DreaM117er/Explorer-Keyboard-RxCT/files/mcu/left-mcu base.stl

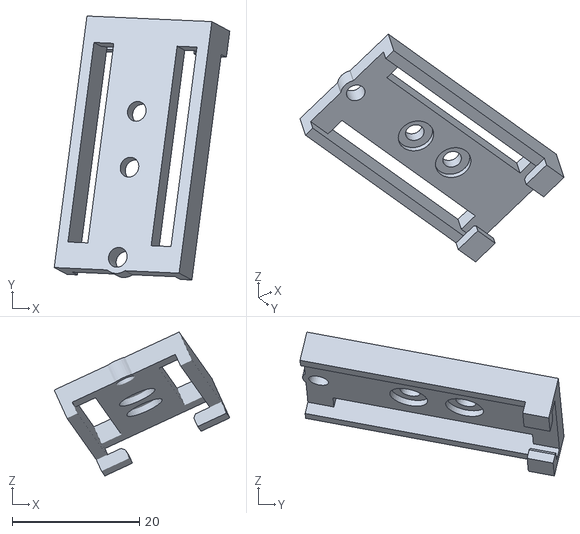
[picture p52: CAD file, 2023-04-23]
files/mcu/left-mcu base.stl
27.6 x 41.6 x 22.7
