DreaM117er/Explorer-Keyboard-RxCT/files/battery/left-box 602050.stl

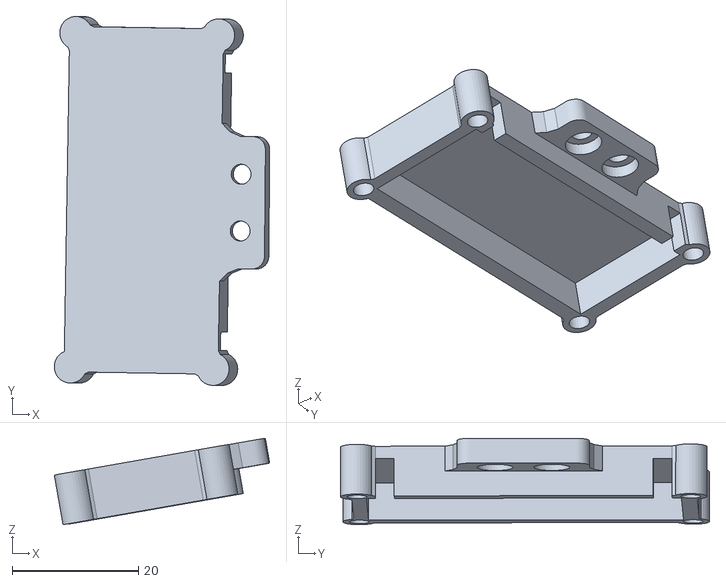
[picture p53: CAD file, 2023-04-23]
files/battery/left-box 602050.stl
34.2 x 58.6 x 13.7
