DreaM117er/Explorer-Keyboard-RxCT/files/mcu/right-trrs stuck.stl

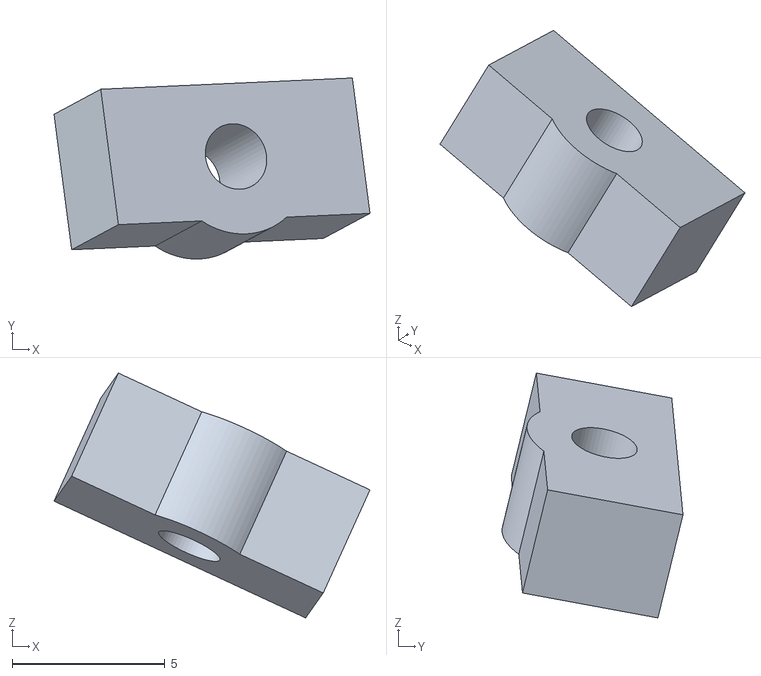
[picture p54: CAD file, 2023-04-23]
files/mcu/right-trrs stuck.stl
10.4 x 5.93 x 8.03
