DreaM117er/Explorer-Keyboard-RxCT/files/thumb/left-thumb area basepart.stl

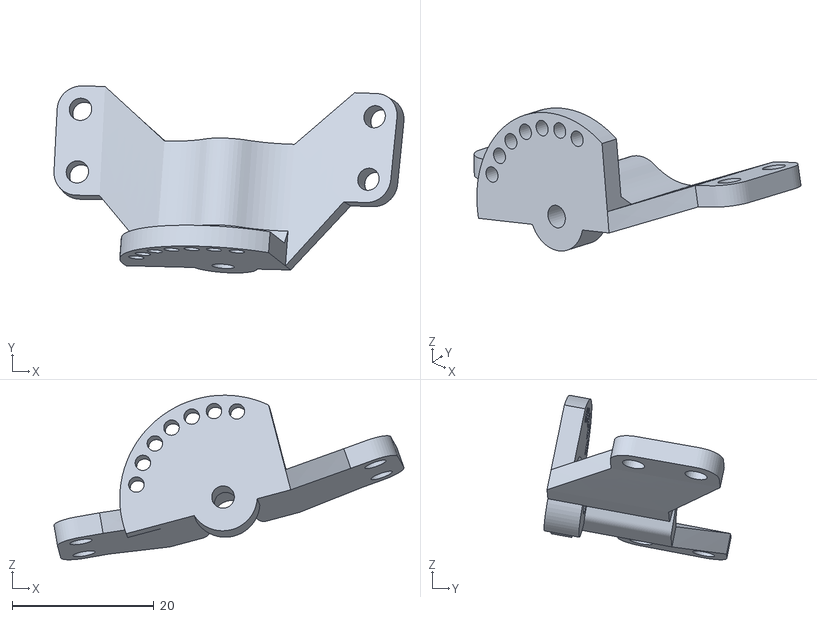
[picture p55: CAD file, 2023-04-23]
files/thumb/left-thumb area basepart.stl
49.4 x 26.4 x 23.2
