DreaM117er/Explorer-Keyboard-RxCT/files/battery/left-box 802050.stl

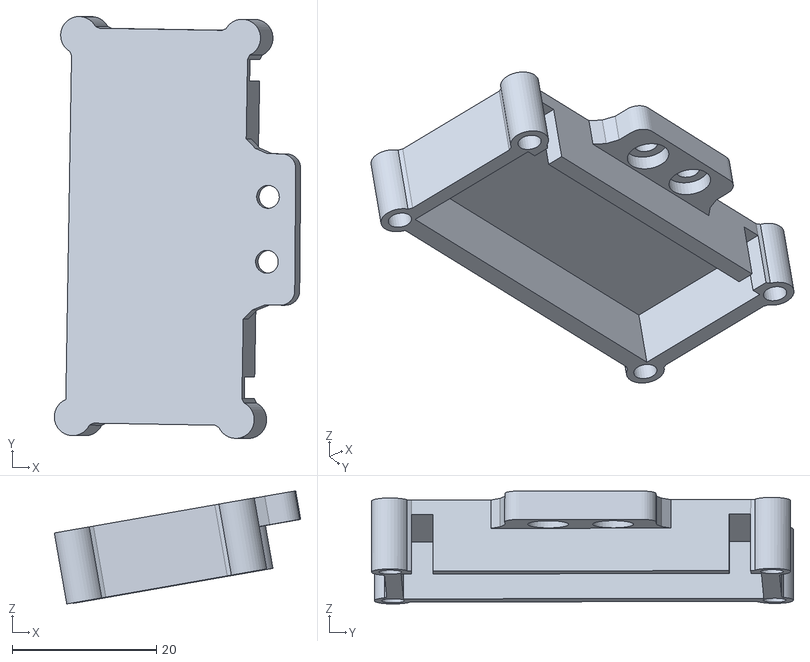
[picture p56: CAD file, 2023-04-23]
files/battery/left-box 802050.stl
34.2 x 58.6 x 15.7
