DreaM117er/Explorer-Keyboard-RxCT/files/thumb/linker.stl

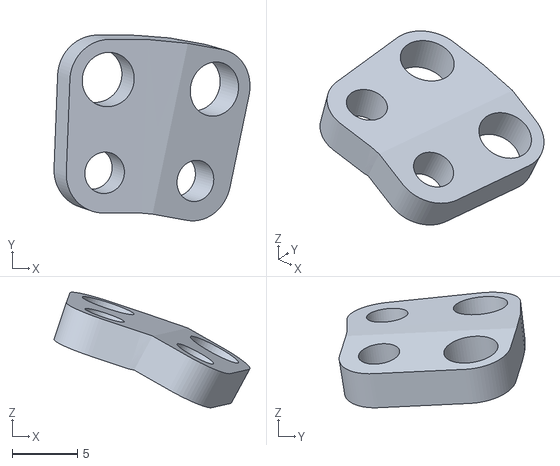
[picture p57: CAD file, 2023-04-23]
files/thumb/linker.stl
15.0 x 14.3 x 8.87
