DreaM117er/Explorer-Keyboard-RxCT/files/right-3x5 bottom case.stl

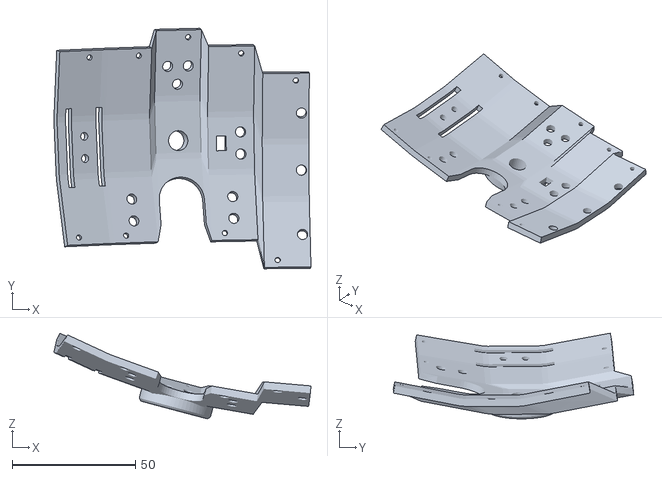
[picture p58: CAD file, 2023-04-23]
files/right-3x5 bottom case.stl
104.4 x 97.8 x 34.8
