DreaM117er/Explorer-Keyboard-RxCT/files/thumb/left-thumb AA plate.stl

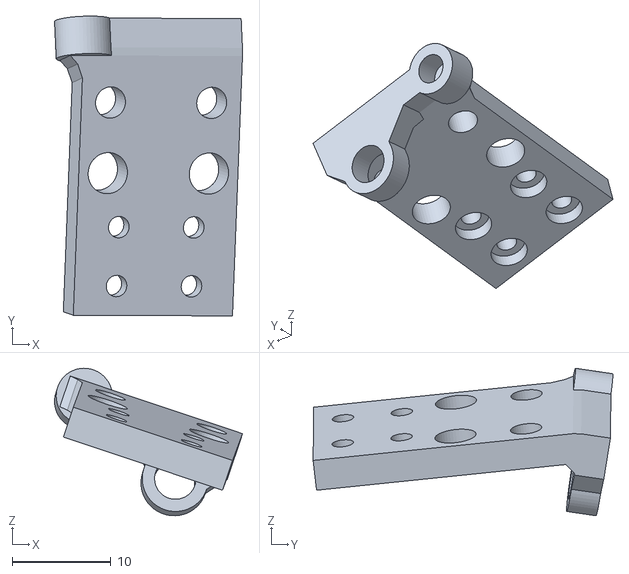
[picture p59: CAD file, 2023-04-23]
files/thumb/left-thumb AA plate.stl
19.0 x 30.4 x 14.9
