DreaM117er/Explorer-Keyboard-RxCT/files/3x1-column.stl

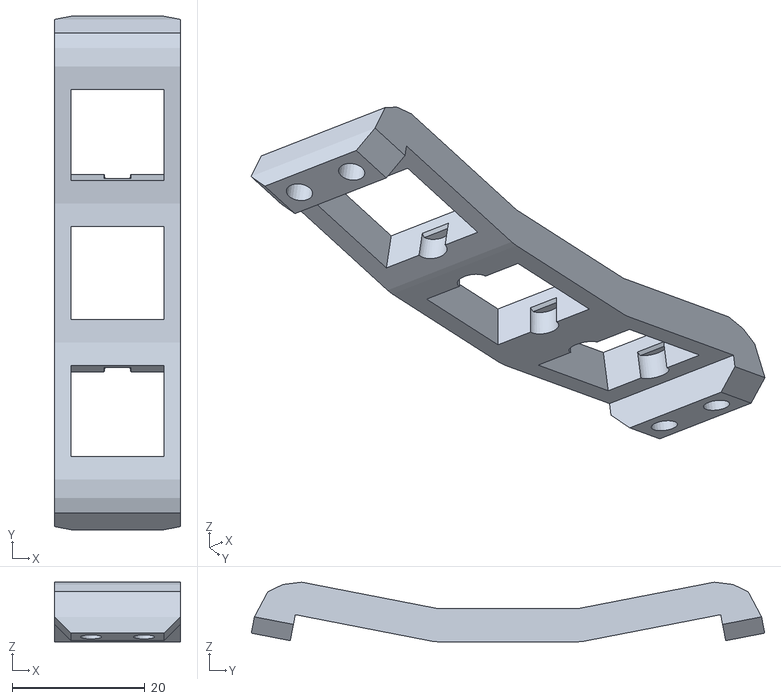
[picture p60: CAD file, 2023-04-23]
files/3x1-column.stl
19.0 x 77.5 x 9.01
