DreaM117er/Explorer-Keyboard-RxCT/files/right-3x1 bottom expand case.stl

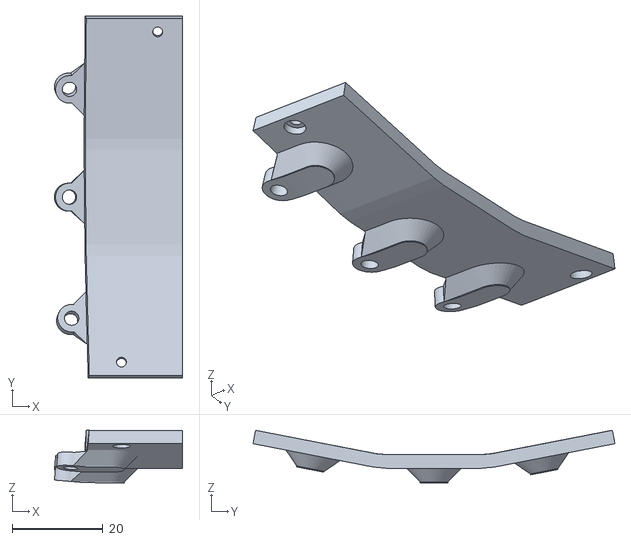
[picture p61: CAD file, 2023-04-23]
files/right-3x1 bottom expand case.stl
28.3 x 79.9 x 11.6
