DreaM117er/Explorer-Keyboard-RxCT/files/thumb/x1-thumb plate.stl

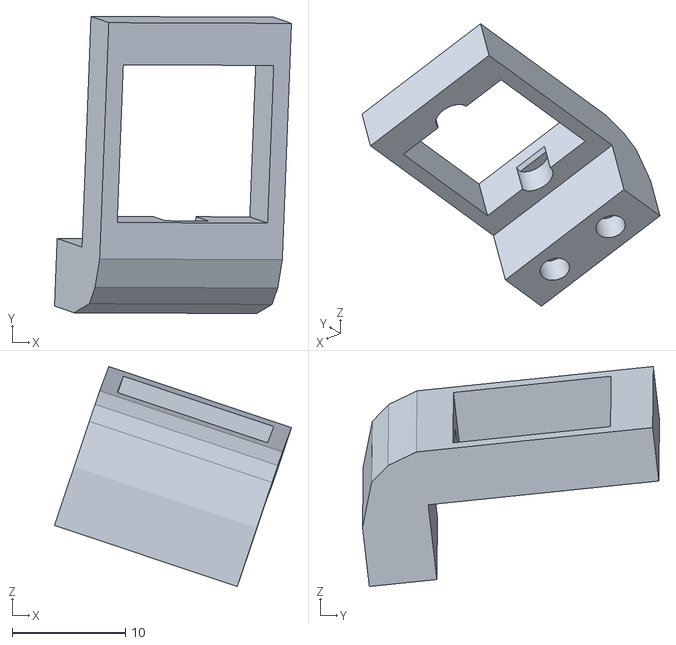
[picture p62: CAD file, 2023-04-23]
files/thumb/x1-thumb plate.stl
20.9 x 26.2 x 19.4
