DreaM117er/Explorer-Keyboard-RxCT/files/right-front basepart.stl

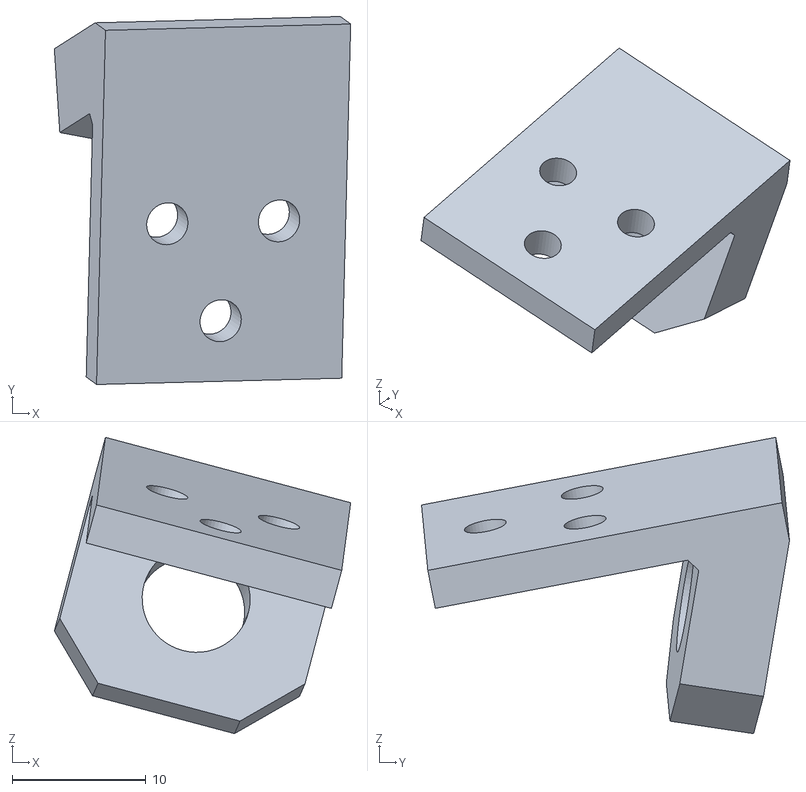
[picture p63: CAD file, 2023-04-23]
files/right-front basepart.stl
22.2 x 27.6 x 22.2
