DreaM117er/Explorer-Keyboard-RxCT/files/4x1-column.stl

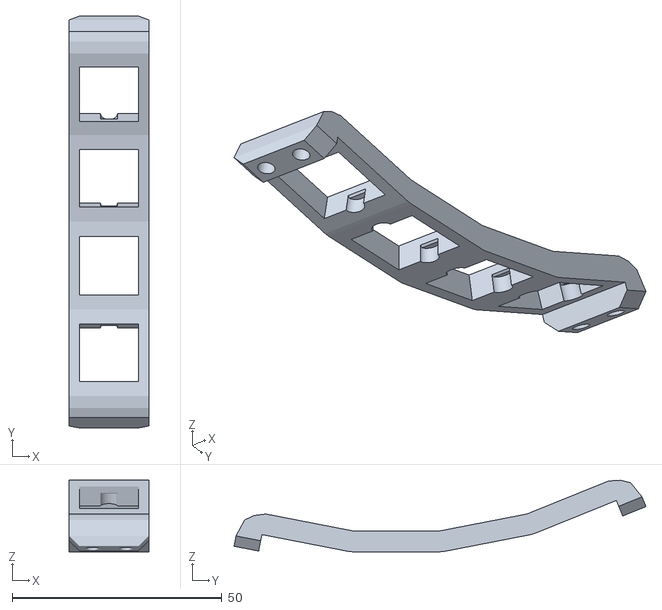
[picture p64: CAD file, 2023-04-23]
files/4x1-column.stl
19.0 x 98.3 x 17.1
