DreaM117er/Explorer-Keyboard-RxCT/image/guide/6-46.jpg

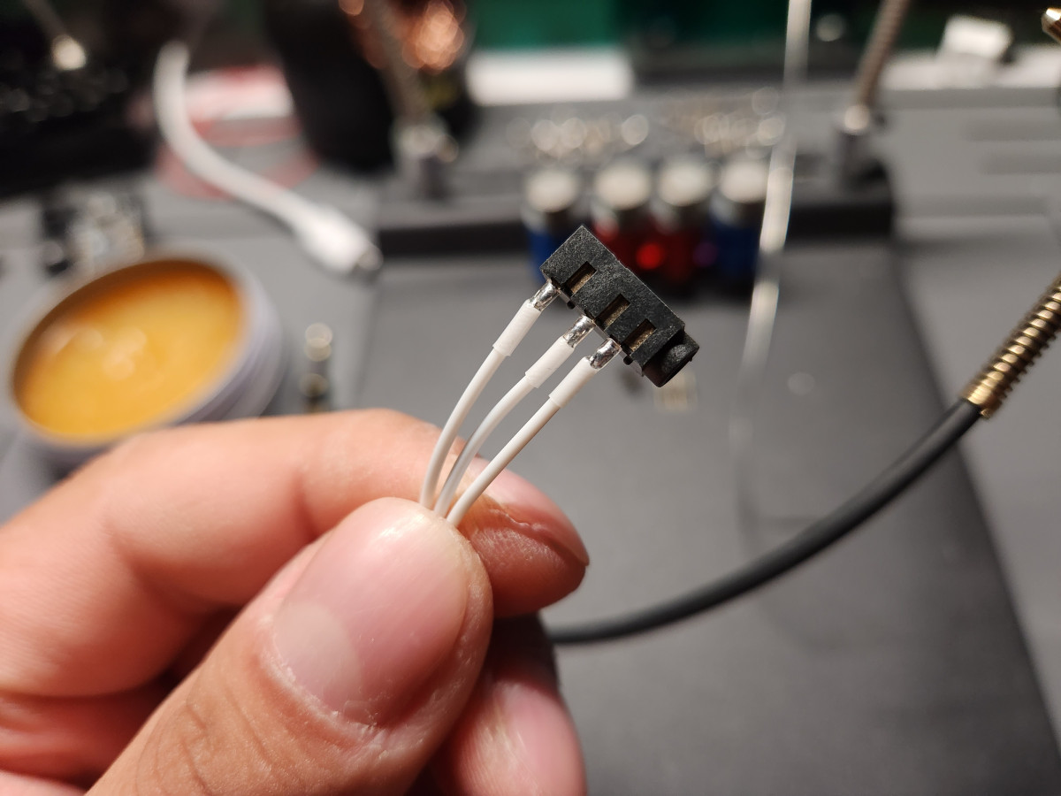
image/guide/6-46.jpg
